aryanprabhuin-ship-it/MechaCore/Images/back-copper.png

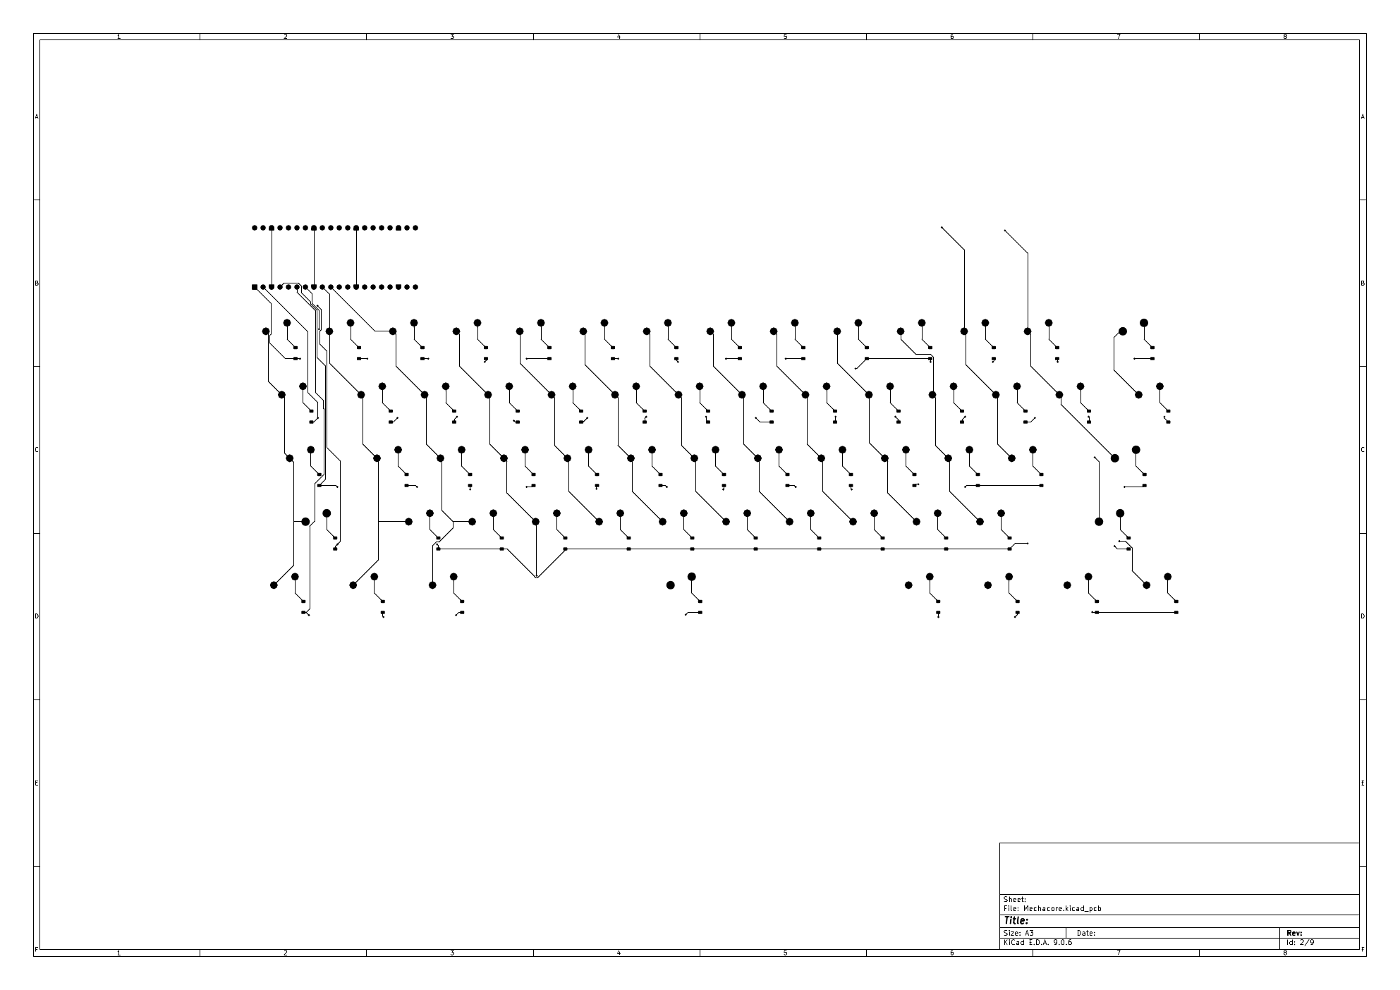
Images/back-copper.png
