aryanprabhuin-ship-it/MechaCore/Images/edge-cuts.png

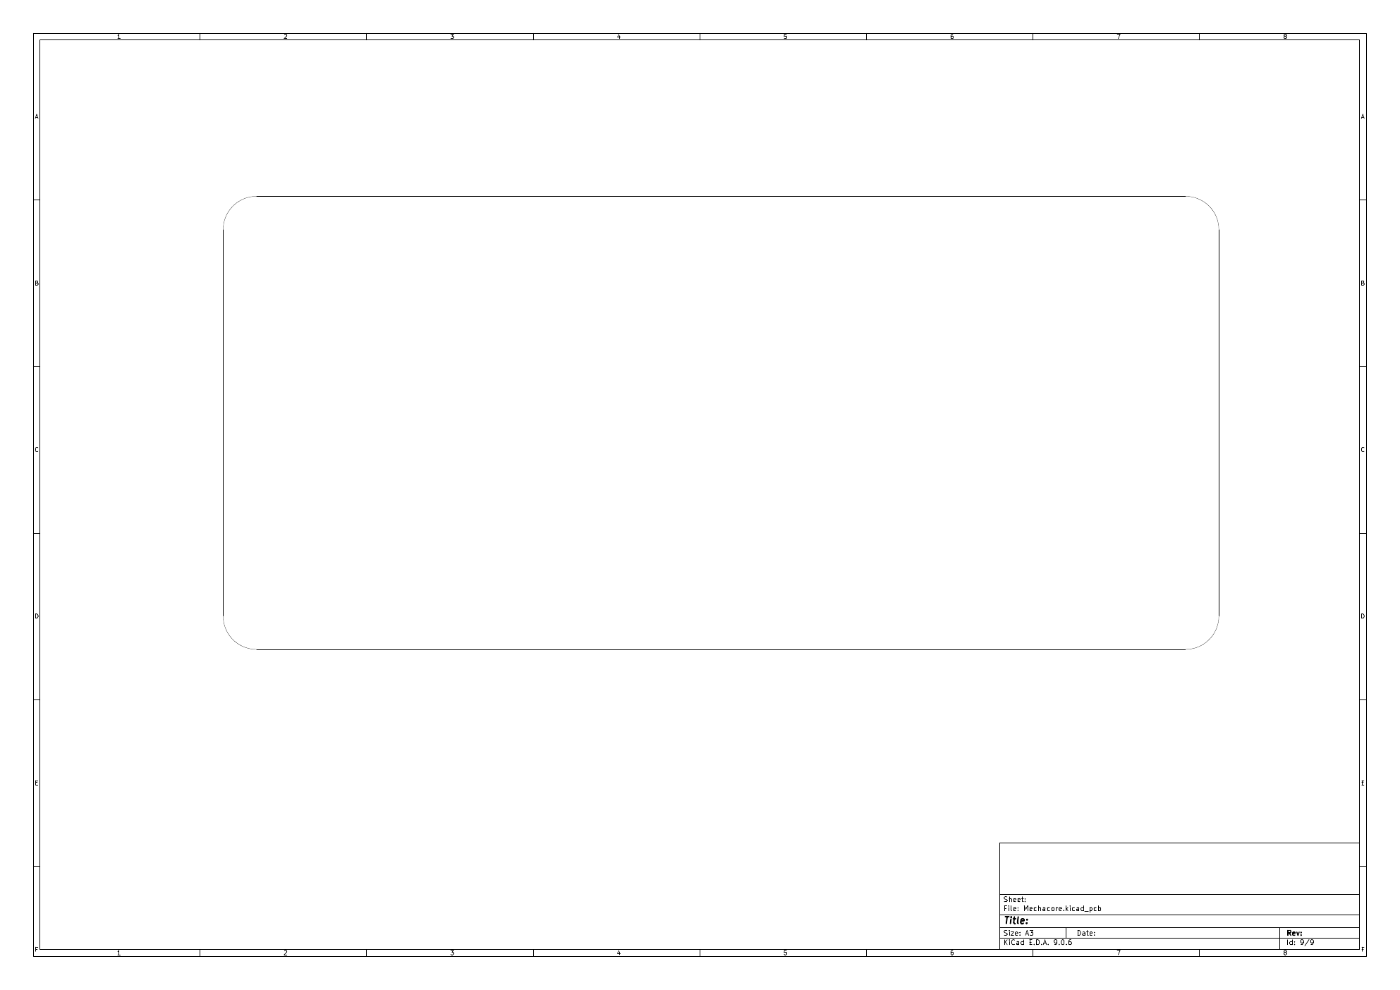
Images/edge-cuts.png
