aryanprabhuin-ship-it/MechaCore/Images/final-pcb-view.png

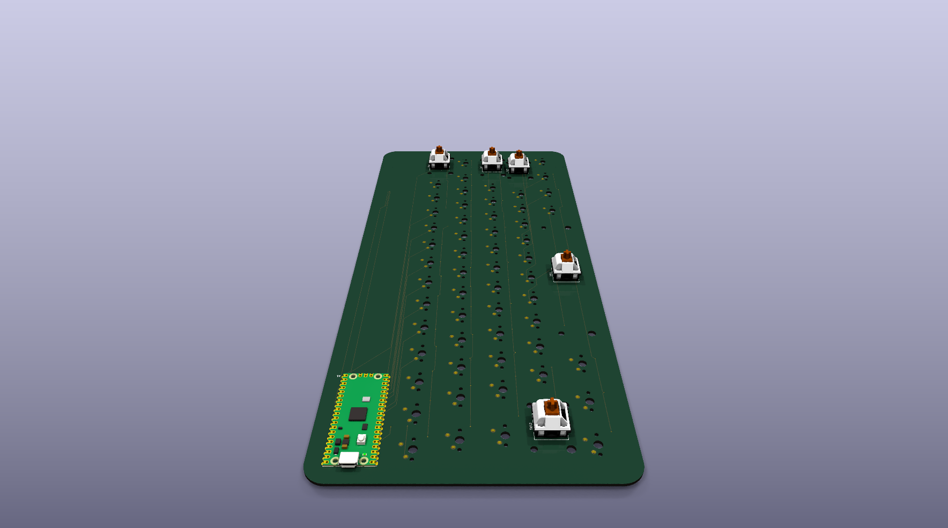
Images/final-pcb-view.png
