aryanprabhuin-ship-it/MechaCore/Images/fresh-pcb-3d-iso.jpg

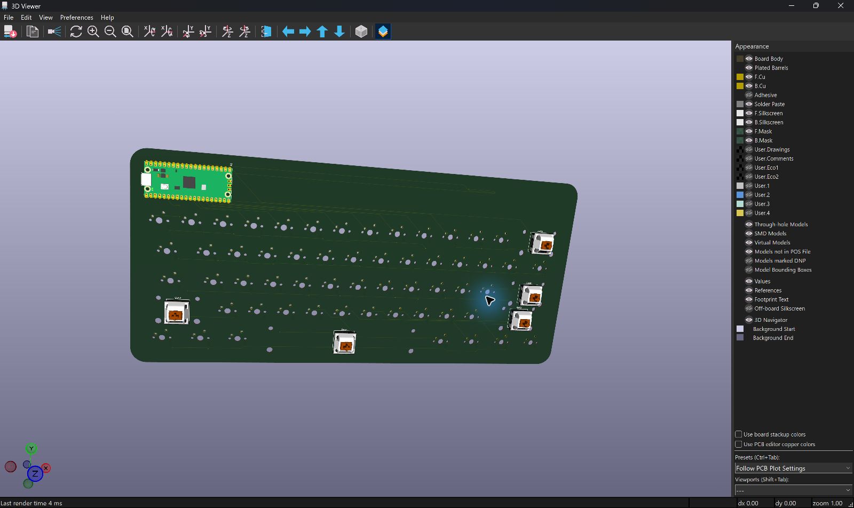
Images/fresh-pcb-3d-iso.jpg
