aryanprabhuin-ship-it/MechaCore/Images/front-copper.png

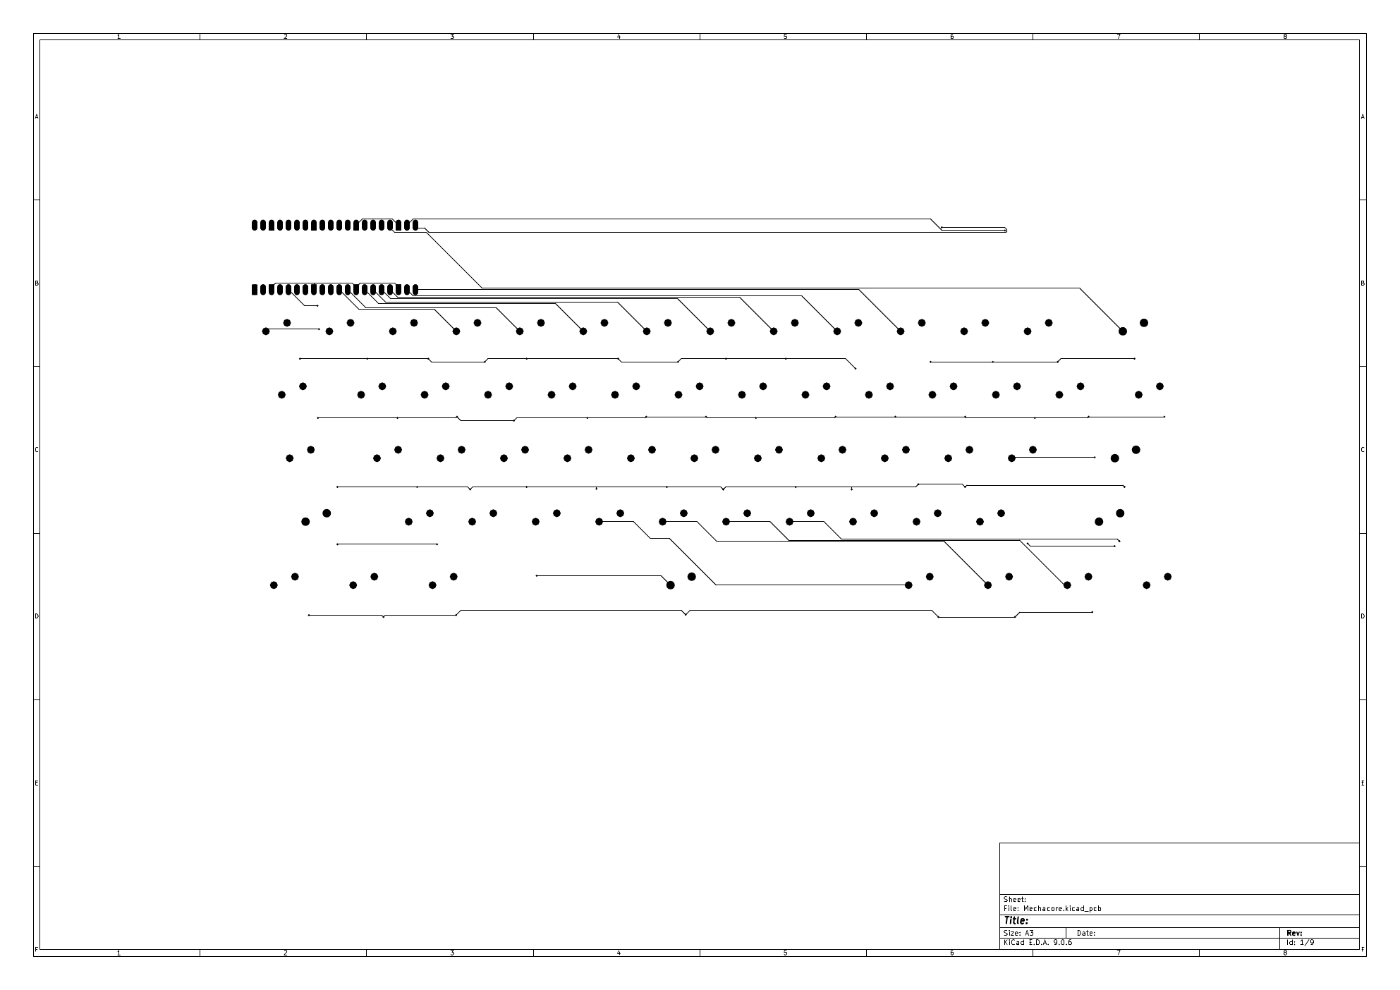
Images/front-copper.png
