aryanprabhuin-ship-it/MechaCore/Images/front-mask.png

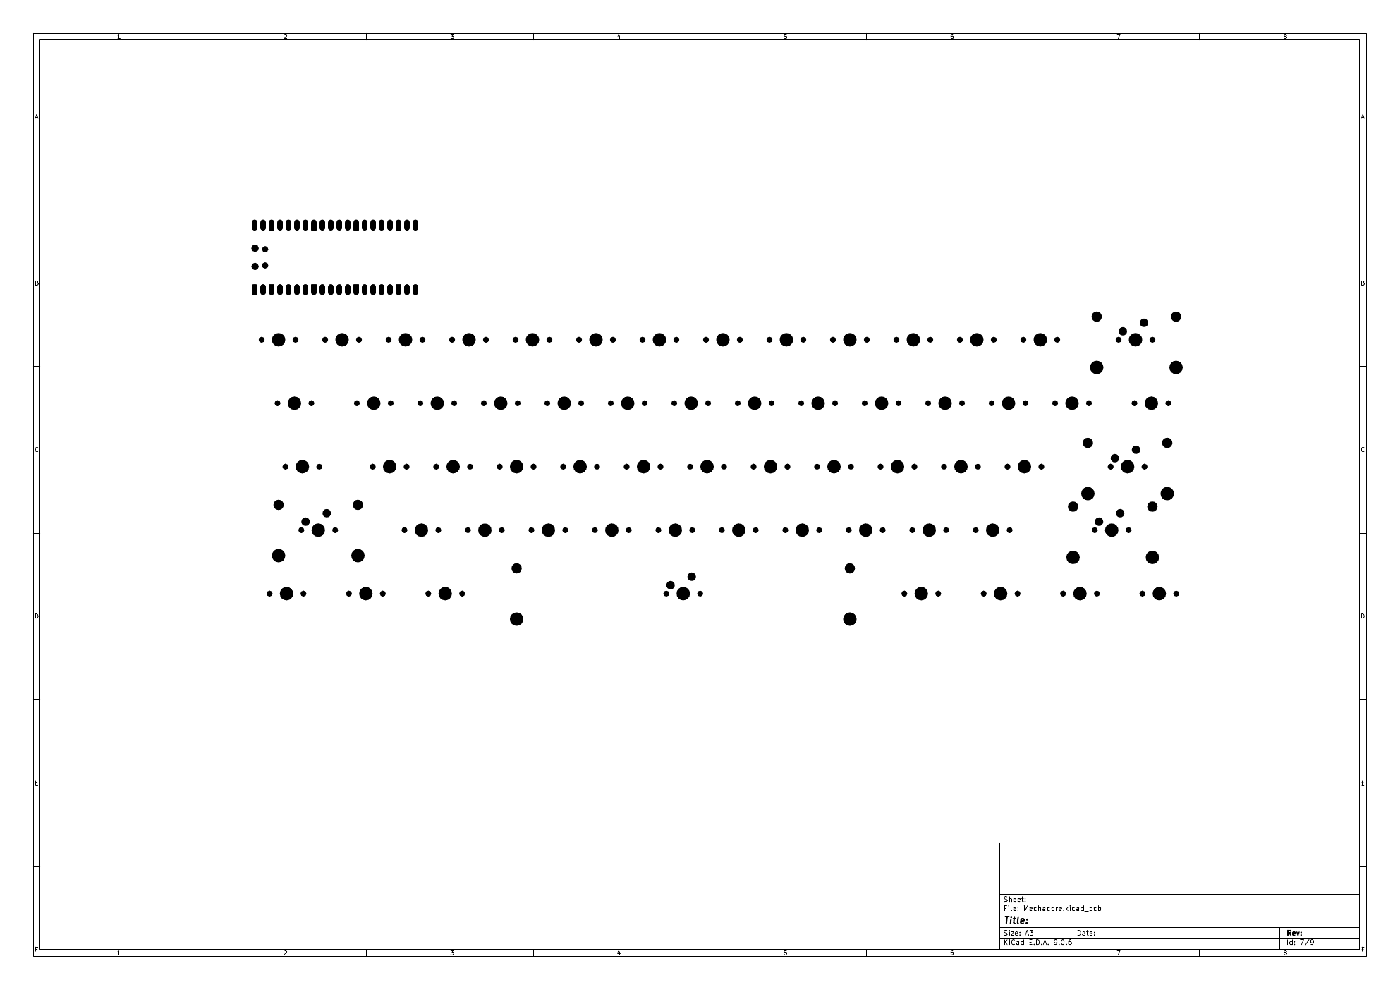
Images/front-mask.png
