aryanprabhuin-ship-it/MechaCore/Images/front-silkscreen.png

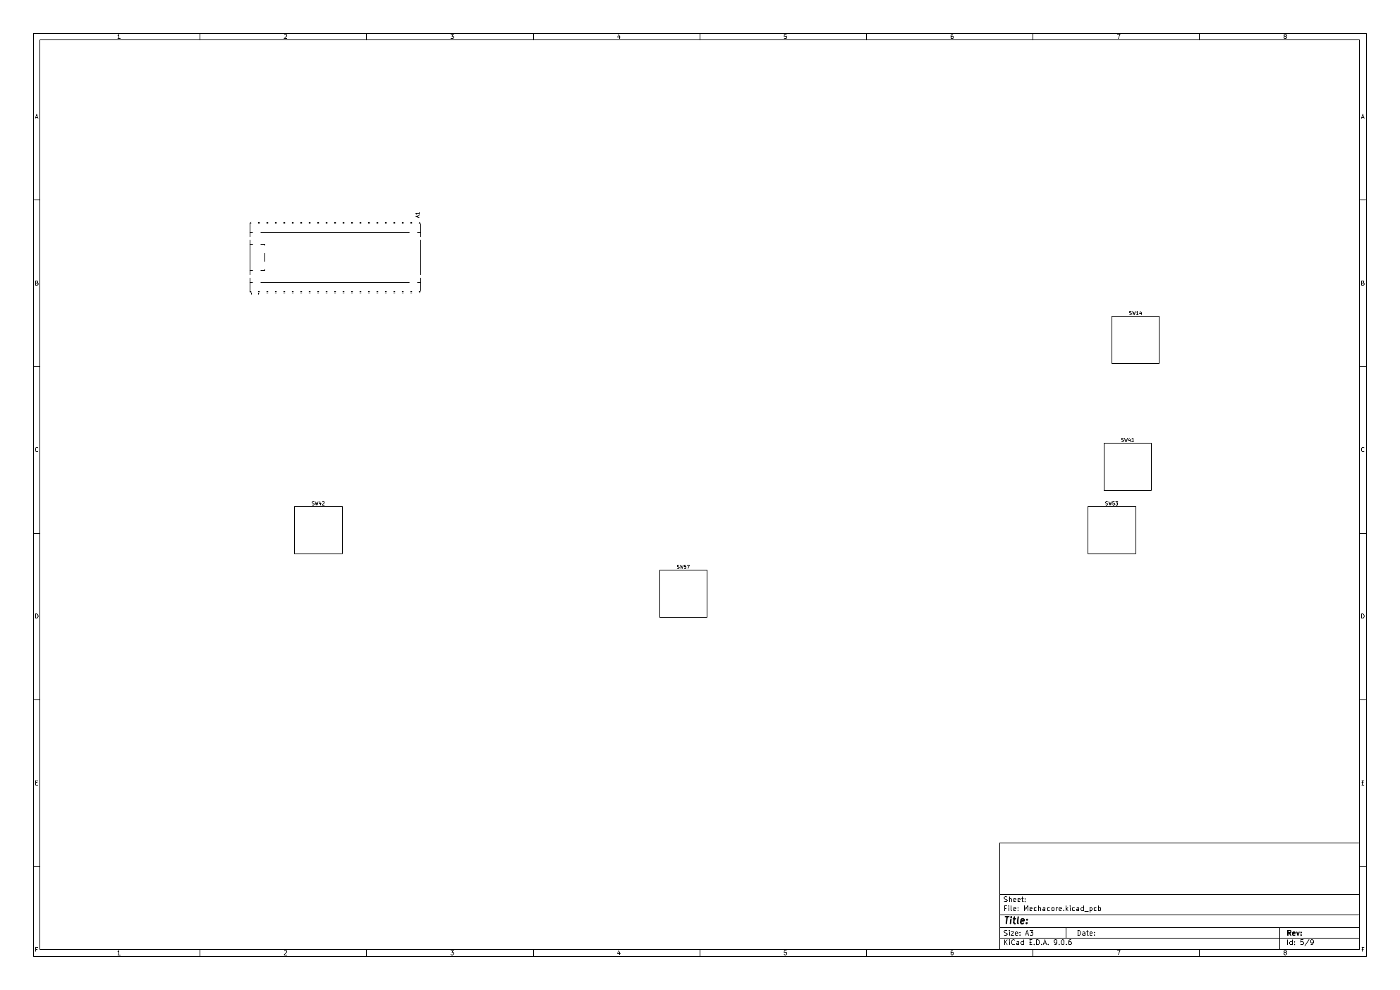
Images/front-silkscreen.png
