aryanprabhuin-ship-it/MechaCore/Images/fusion-case.png

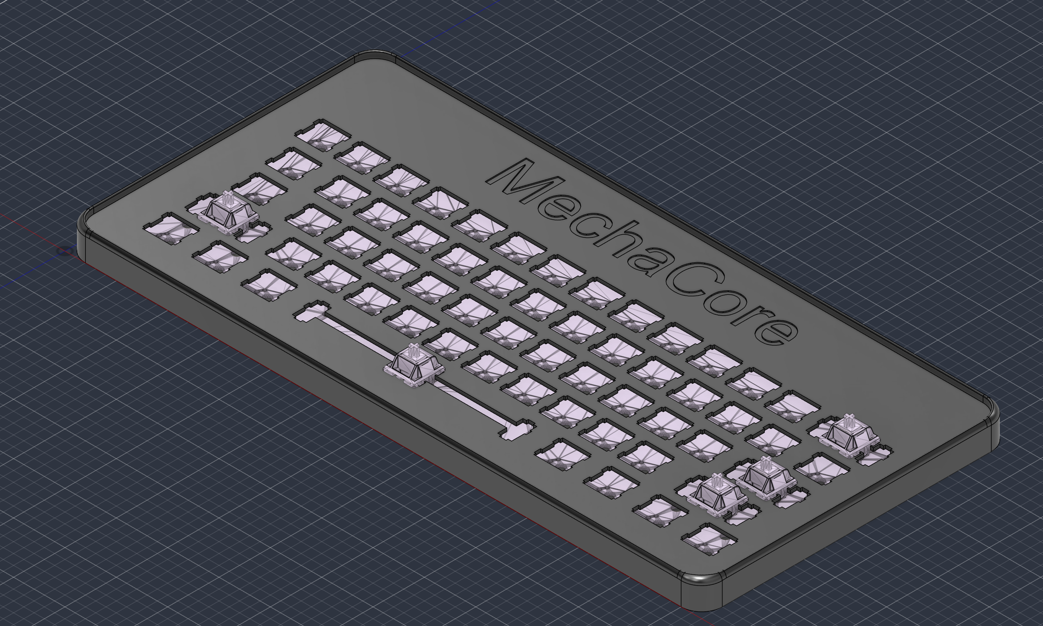
Images/fusion-case.png
