aryanprabhuin-ship-it/MechaCore/Images/mounting-system-case-interior-top.png

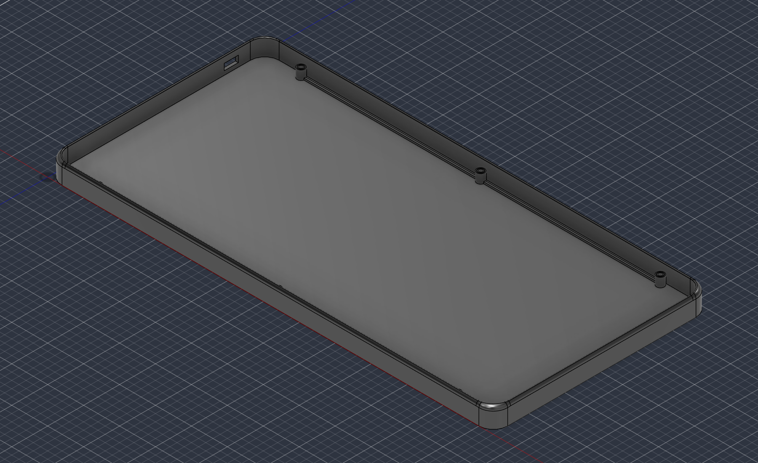
Images/mounting-system-case-interior-top.png
