aryanprabhuin-ship-it/MechaCore/Images/mounting-system-fastener-detail.png

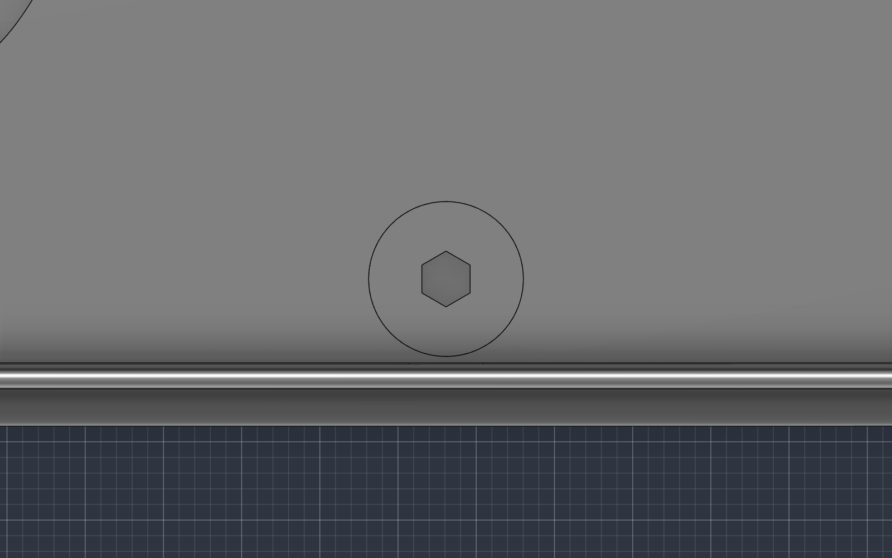
Images/mounting-system-fastener-detail.png
