aryanprabhuin-ship-it/MechaCore/Images/pcb-3d-bottom.png

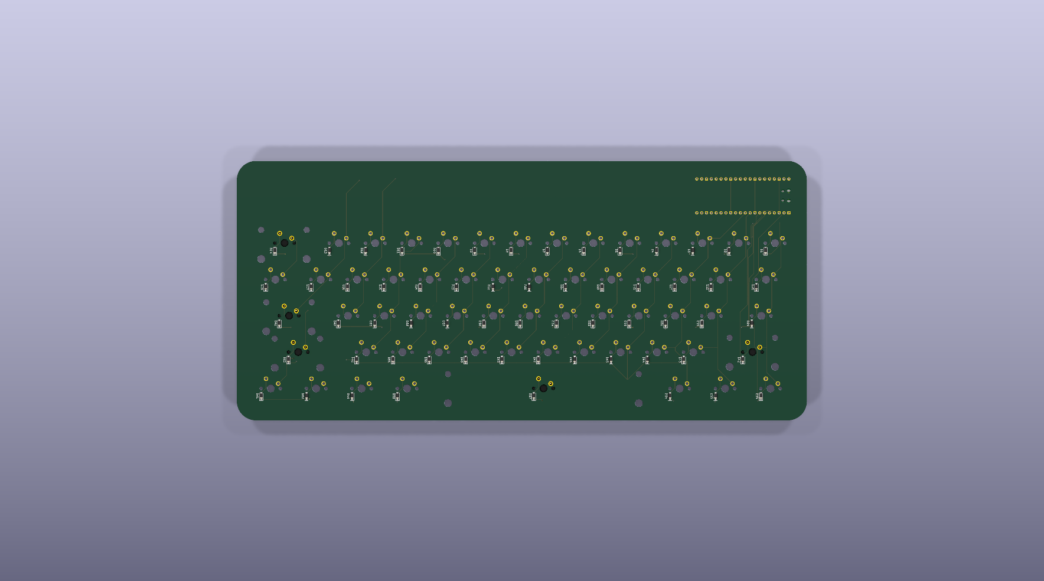
Images/pcb-3d-bottom.png
