aryanprabhuin-ship-it/MechaCore/Images/pcb-3d-top.png

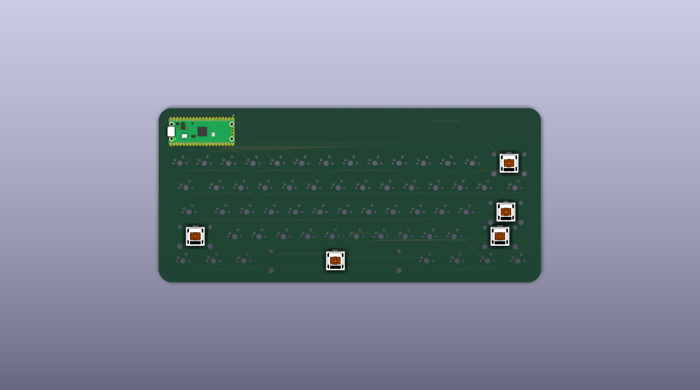
Images/pcb-3d-top.png
