aryanprabhuin-ship-it/MechaCore/Images/pcb-back-profile.png

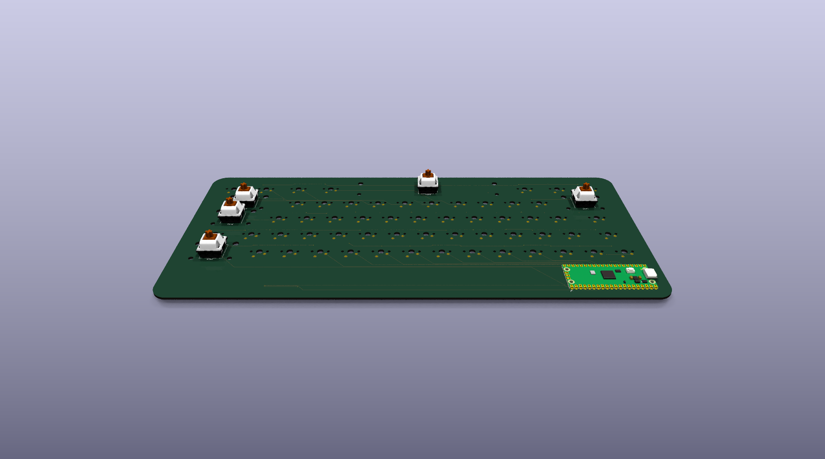
Images/pcb-back-profile.png
