aryanprabhuin-ship-it/MechaCore/Images/pcb-editor-routed.png

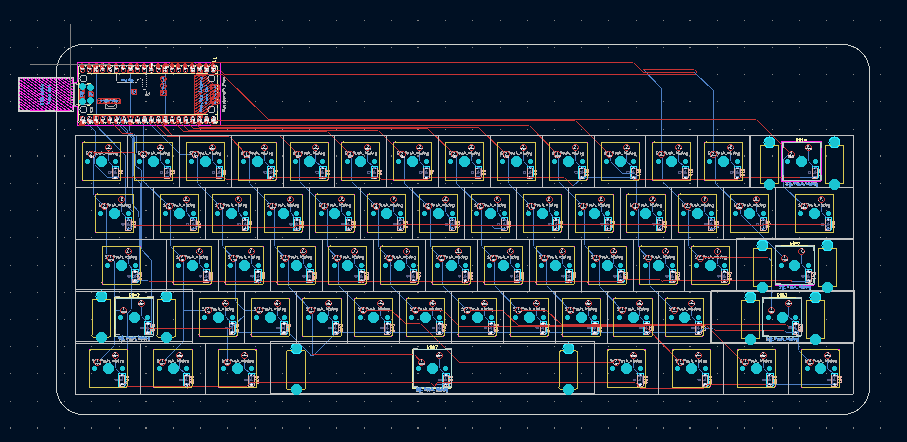
Images/pcb-editor-routed.png
