aryanprabhuin-ship-it/MechaCore/Images/pcb-front-profile.png

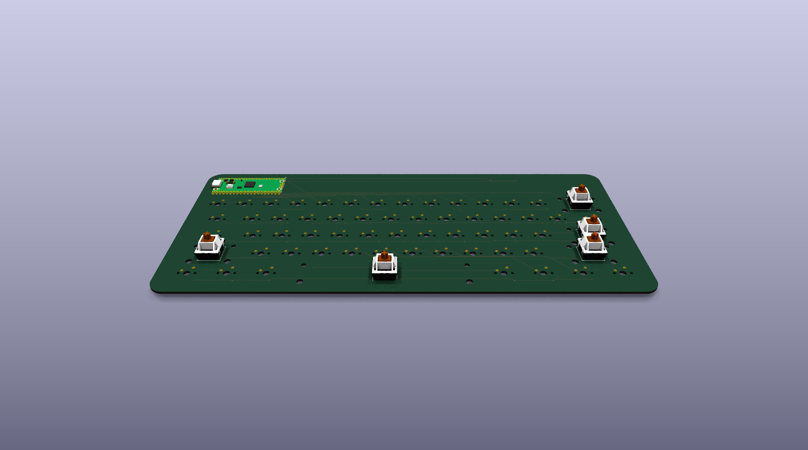
Images/pcb-front-profile.png
