aryanprabhuin-ship-it/MechaCore/Images/pcb-quote.png

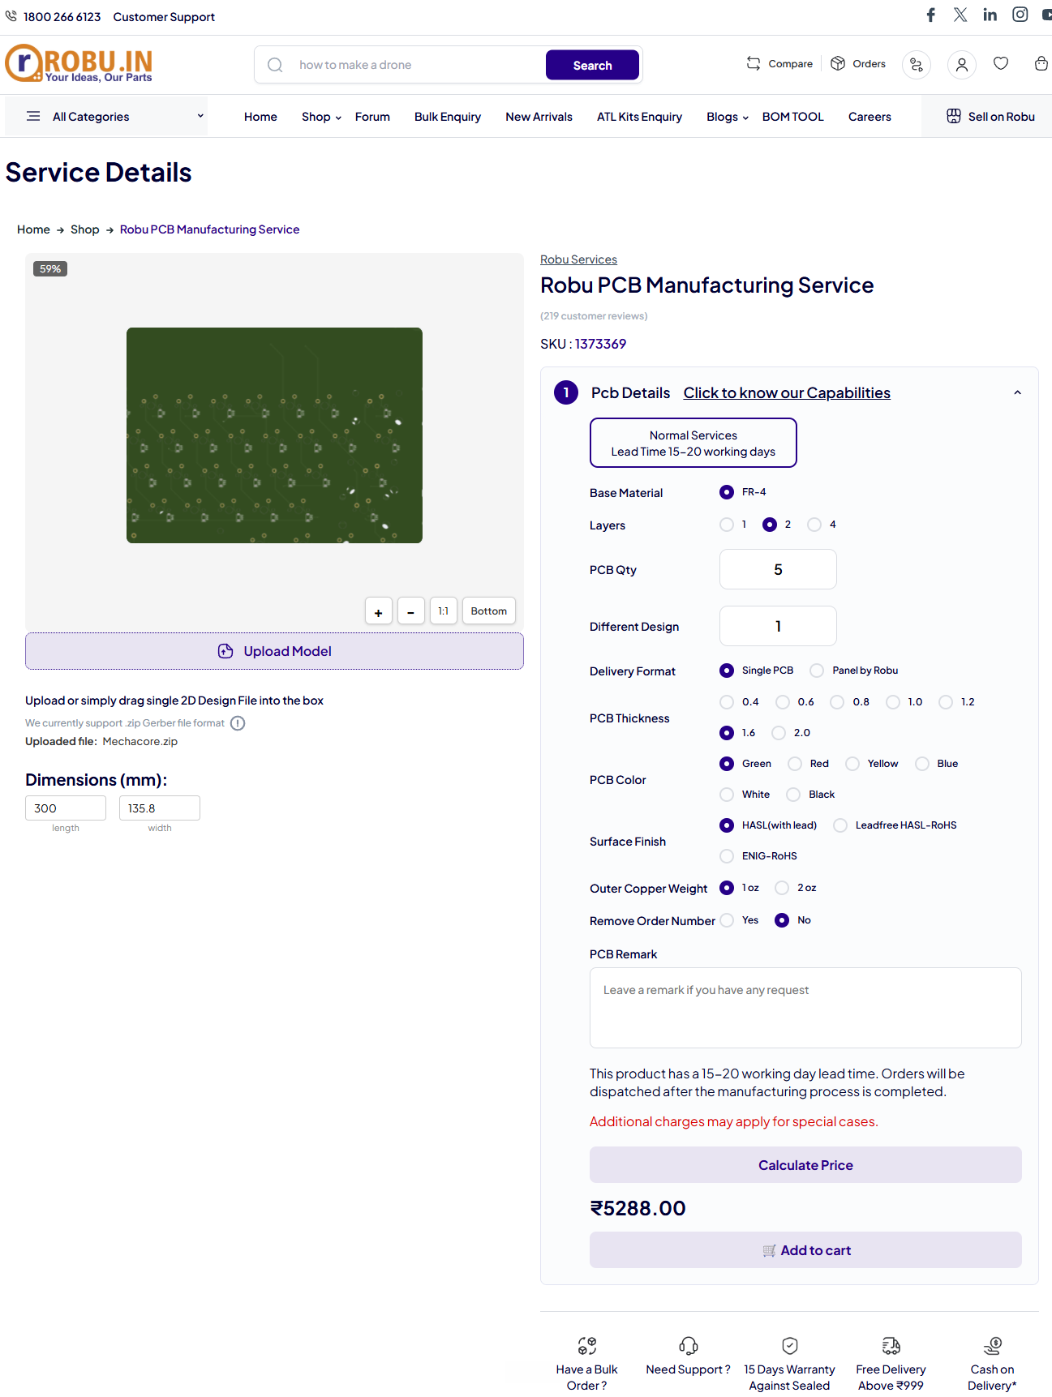
Images/pcb-quote.png
