aryanprabhuin-ship-it/MechaCore/Images/pico-clearance.png

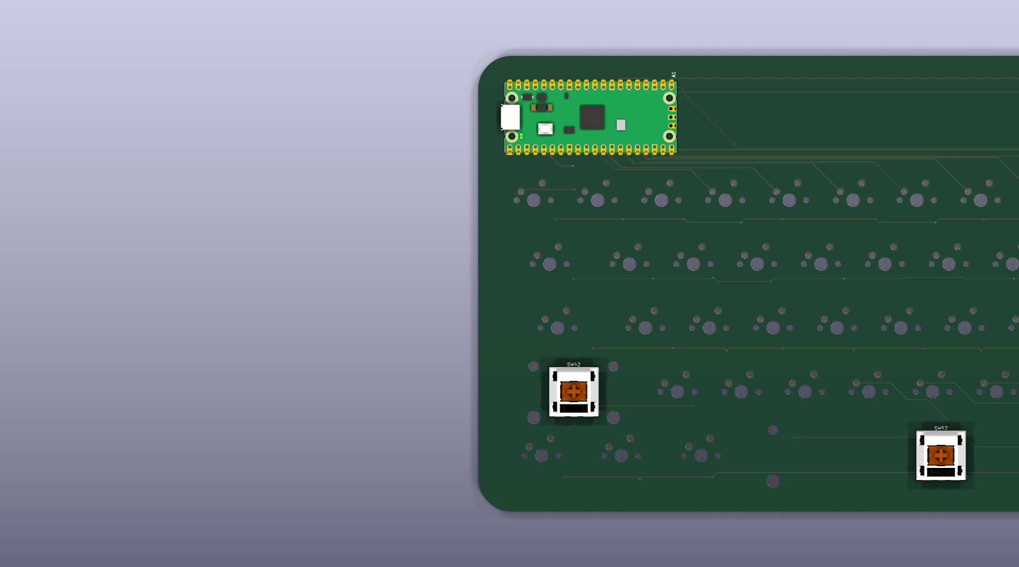
Images/pico-clearance.png
