aryanprabhuin-ship-it/MechaCore/Images/pico-diode-cart.png

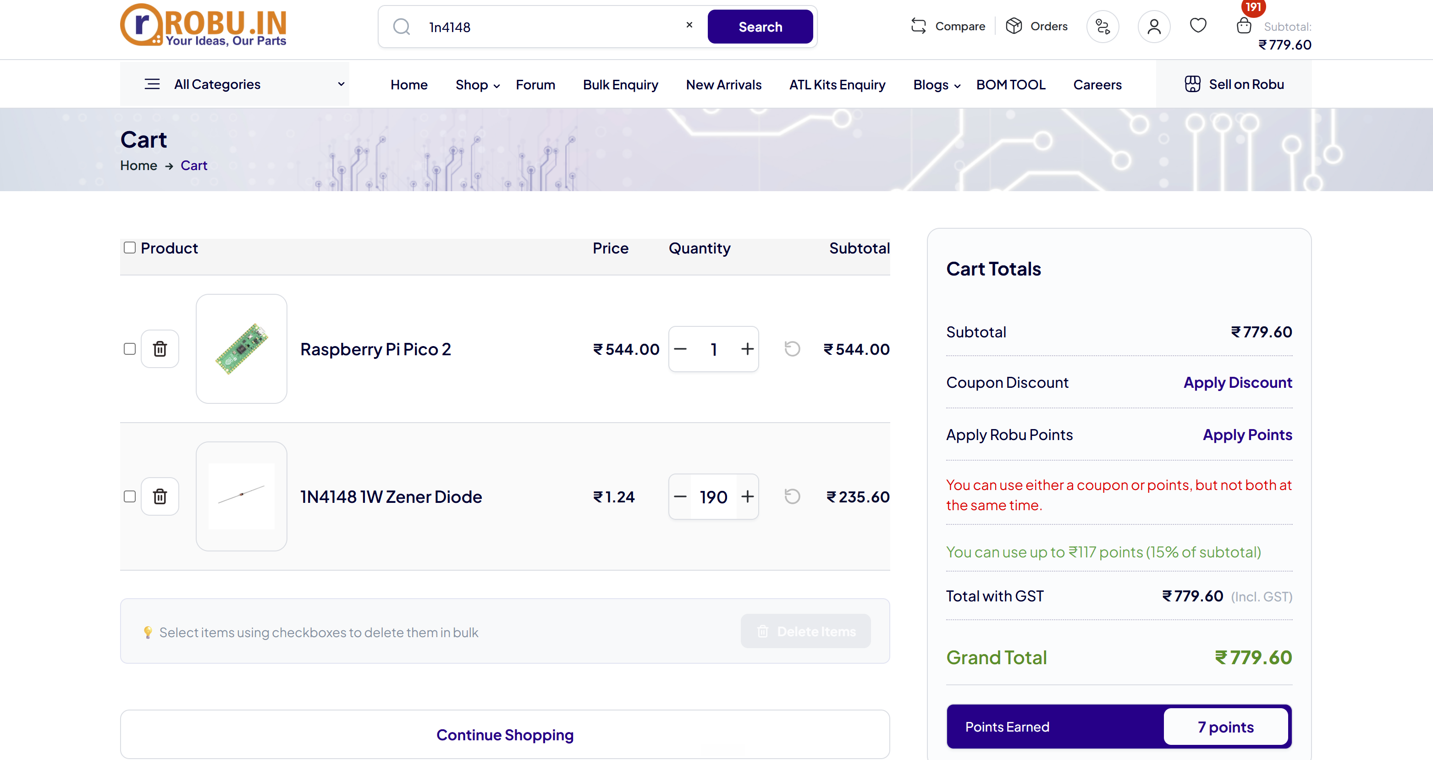
Images/pico-diode-cart.png
