aryanprabhuin-ship-it/MechaCore/Images/revC-engineered-interior-top.png

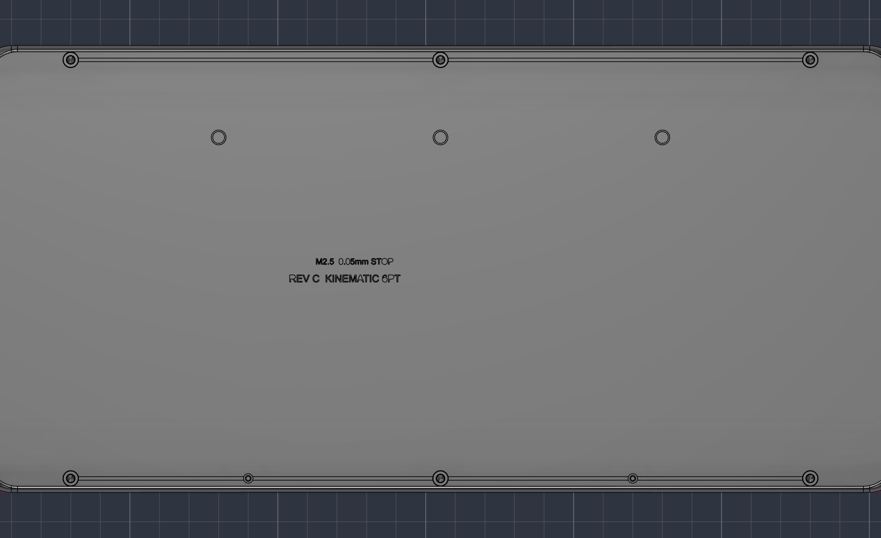
Images/revC-engineered-interior-top.png
