aryanprabhuin-ship-it/MechaCore/Images/revD-snap-collet-plate-underside.png

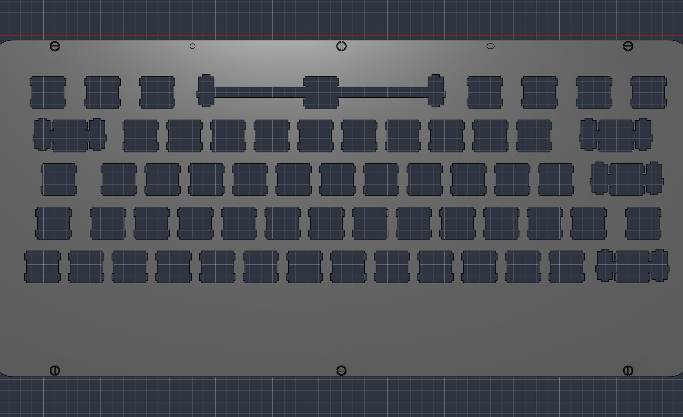
Images/revD-snap-collet-plate-underside.png
