aryanprabhuin-ship-it/MechaCore/Images/revD-undercut-socket-detail.png

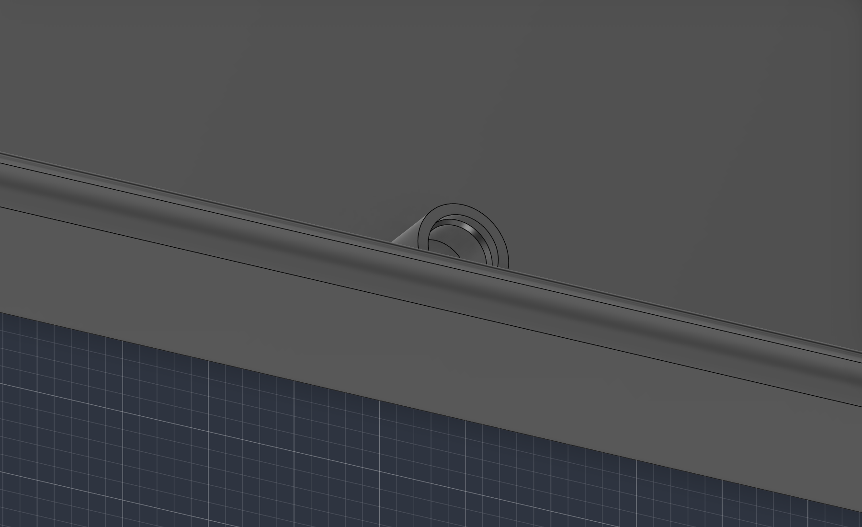
Images/revD-undercut-socket-detail.png
