aryanprabhuin-ship-it/MechaCore/Images/switch-stab-cart.png

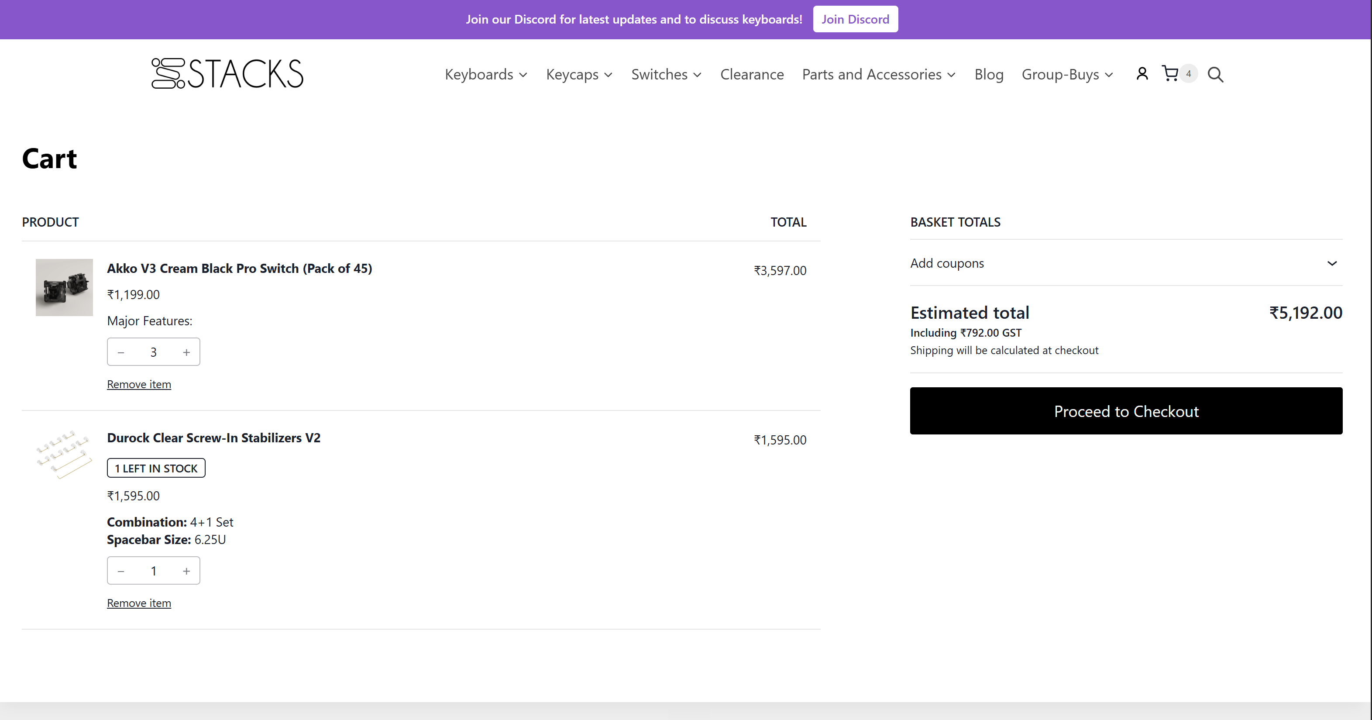
Images/switch-stab-cart.png
