aryanprabhuin-ship-it/MechaCore/Working screen shot/Screenshot 2026-08-01 140303.png

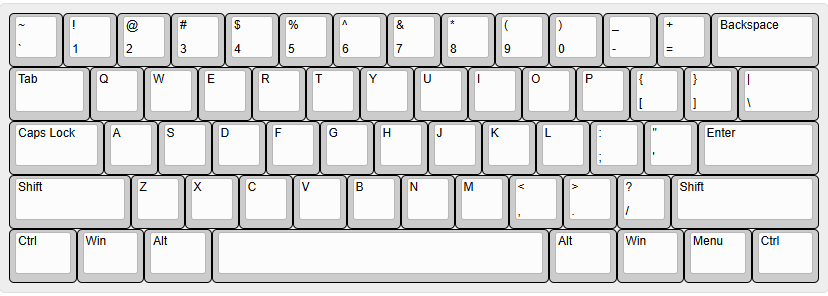
Working screen shot/Screenshot 2026-08-01 140303.png
