aryanprabhuin-ship-it/MechaCore/Working screen shot/Screenshot 2026-08-01 160410.png

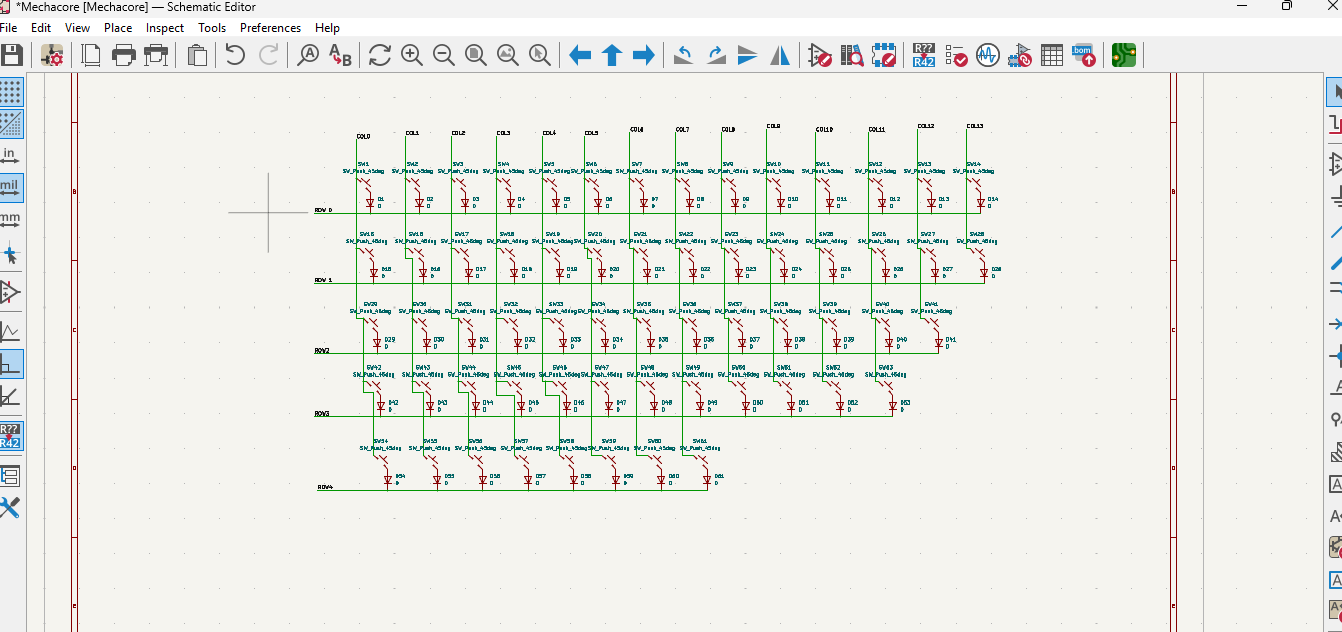
Working screen shot/Screenshot 2026-08-01 160410.png
