aryanprabhuin-ship-it/MechaCore/Working screen shot/Screenshot 2026-08-02 164619.png

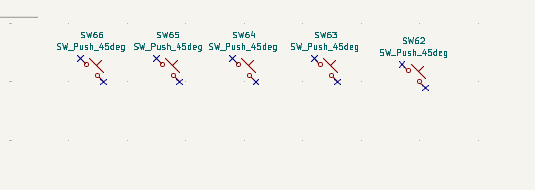
Working screen shot/Screenshot 2026-08-02 164619.png
