aryanprabhuin-ship-it/MechaCore/Images/fresh-pcb-step-top.jpg

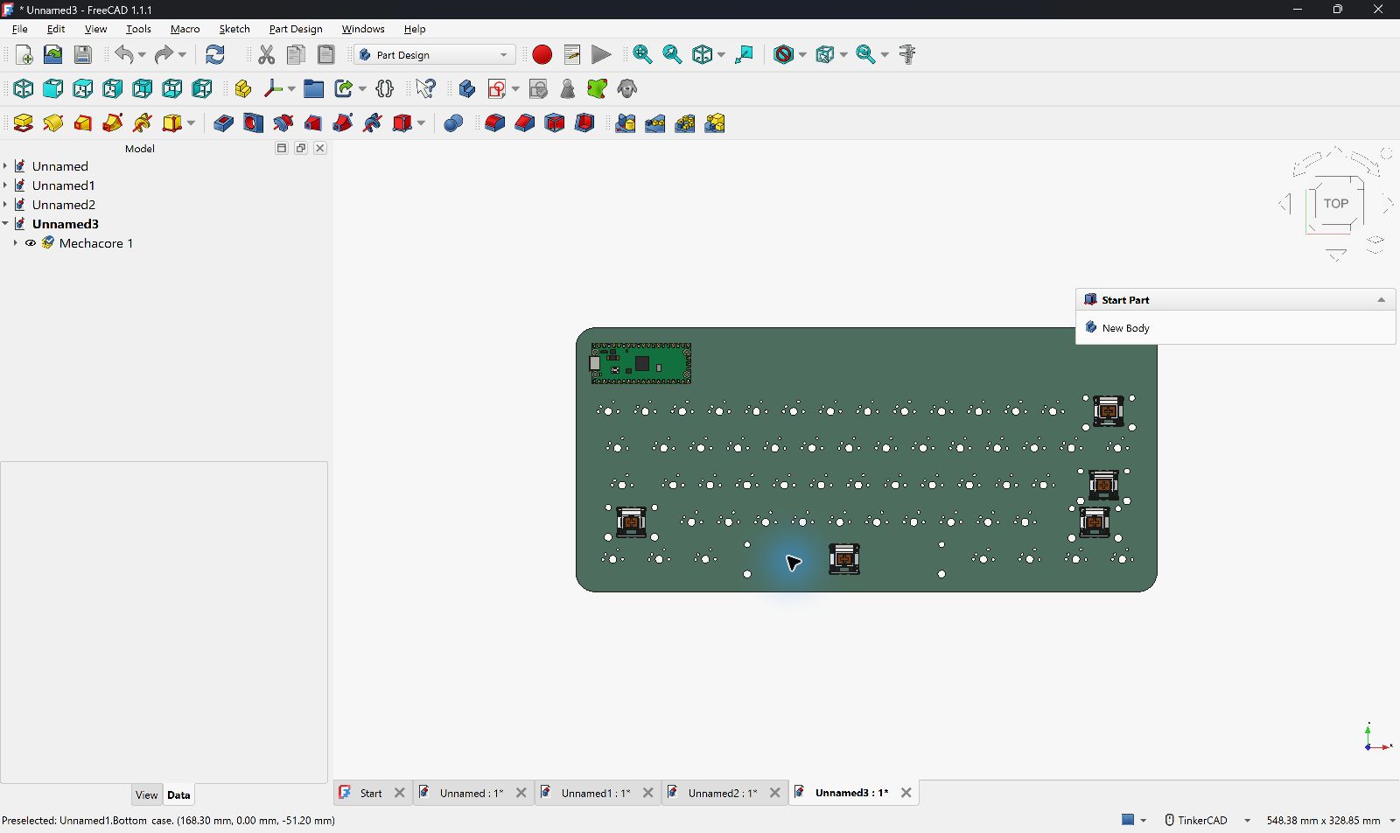
Images/fresh-pcb-step-top.jpg
