aryanprabhuin-ship-it/MechaCore/Images/mounting-system-assembled-iso.png

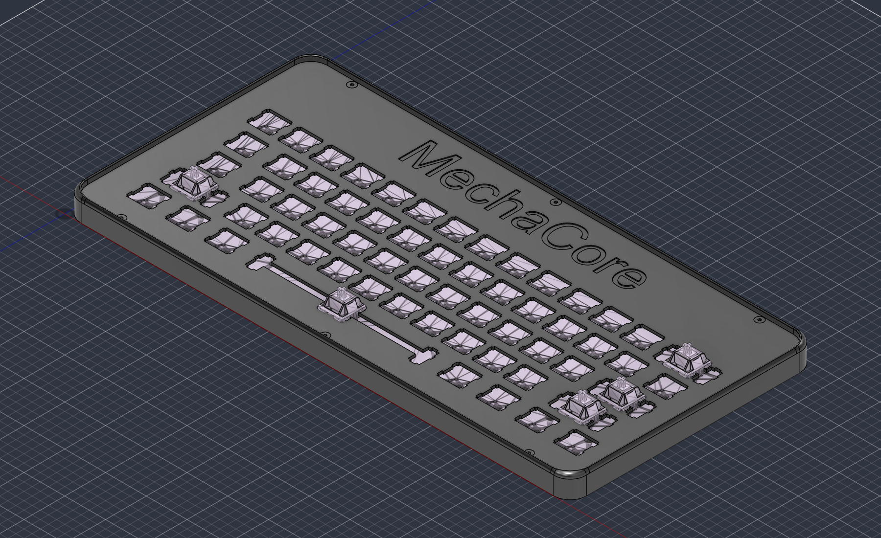
Images/mounting-system-assembled-iso.png
