aryanprabhuin-ship-it/MechaCore/Images/revC-overengineered-assembly-top.png

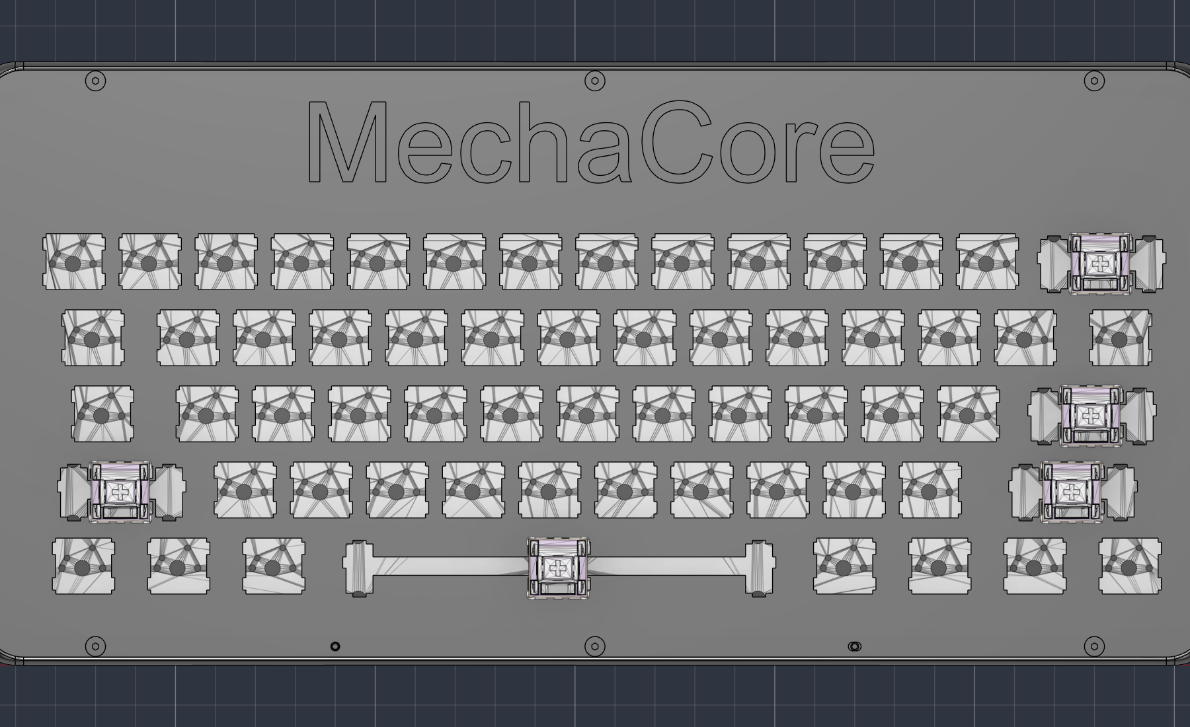
Images/revC-overengineered-assembly-top.png
